dccharacter/RF3Sens/doc/RFSens.sch

## EAGLE design doc/RFSens.sch (2017-03-08)

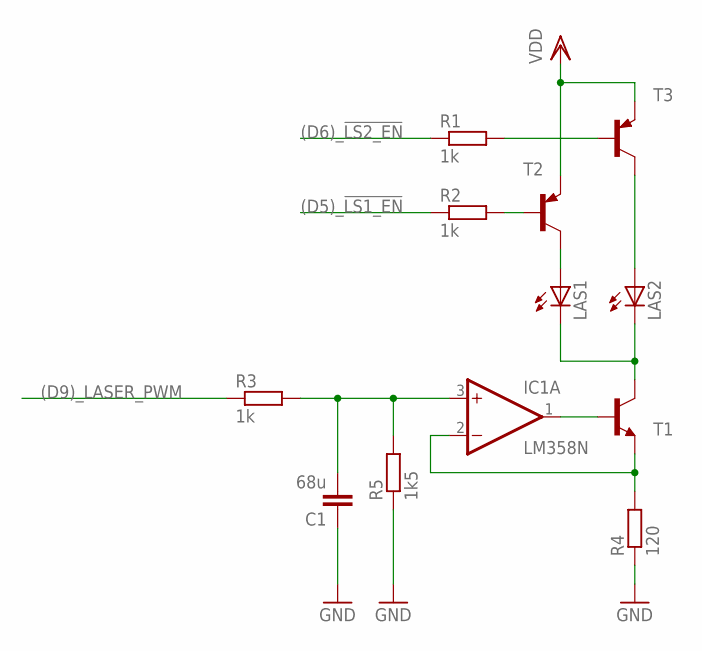
[picture p6: schematic RFSens.sch]

Parts:
C1: 68u; C5B3.5
IC1: LM358N; DIL08
LAS1, LAS2: LED; SMARTLED-TTW
R1, R2, R3: 1k; 0204/5
R4: 120; 0204/5
R5: 1k5; 0204/5
T1: -NPN-SOT89-BCE; SOT89-BCE
T2, T3: -PNP-SOT23-EBC; SOT23-EBC

Connections:
(D5)_!LS1_EN!: R2.1
(D6)_!LS2_EN!: R1.1
(D9)_LASER_PWM: R3.1
GND: C1.1, R4.1, R5.1
unnamed: IC1.2 (-IN), R4.2, T1.E
unnamed: IC1.1 (OUT), T1.B
unnamed: C1.2, IC1.3 (+IN), R3.2, R5.2
unnamed: LAS1.C@1 (C), LAS2.C@1 (C), T1.C
unnamed: R1.2, T3.B
unnamed: LAS2.A@1 (A), T3.C
unnamed: LAS1.A@1 (A), T2.C
unnamed: R2.2, T2.B
VDD: T2.E, T3.E
