dccharacter/RF3Sens/doc/digispark_adns2620.sch

## EAGLE design doc/digispark_adns2620.sch (2016-02-06)

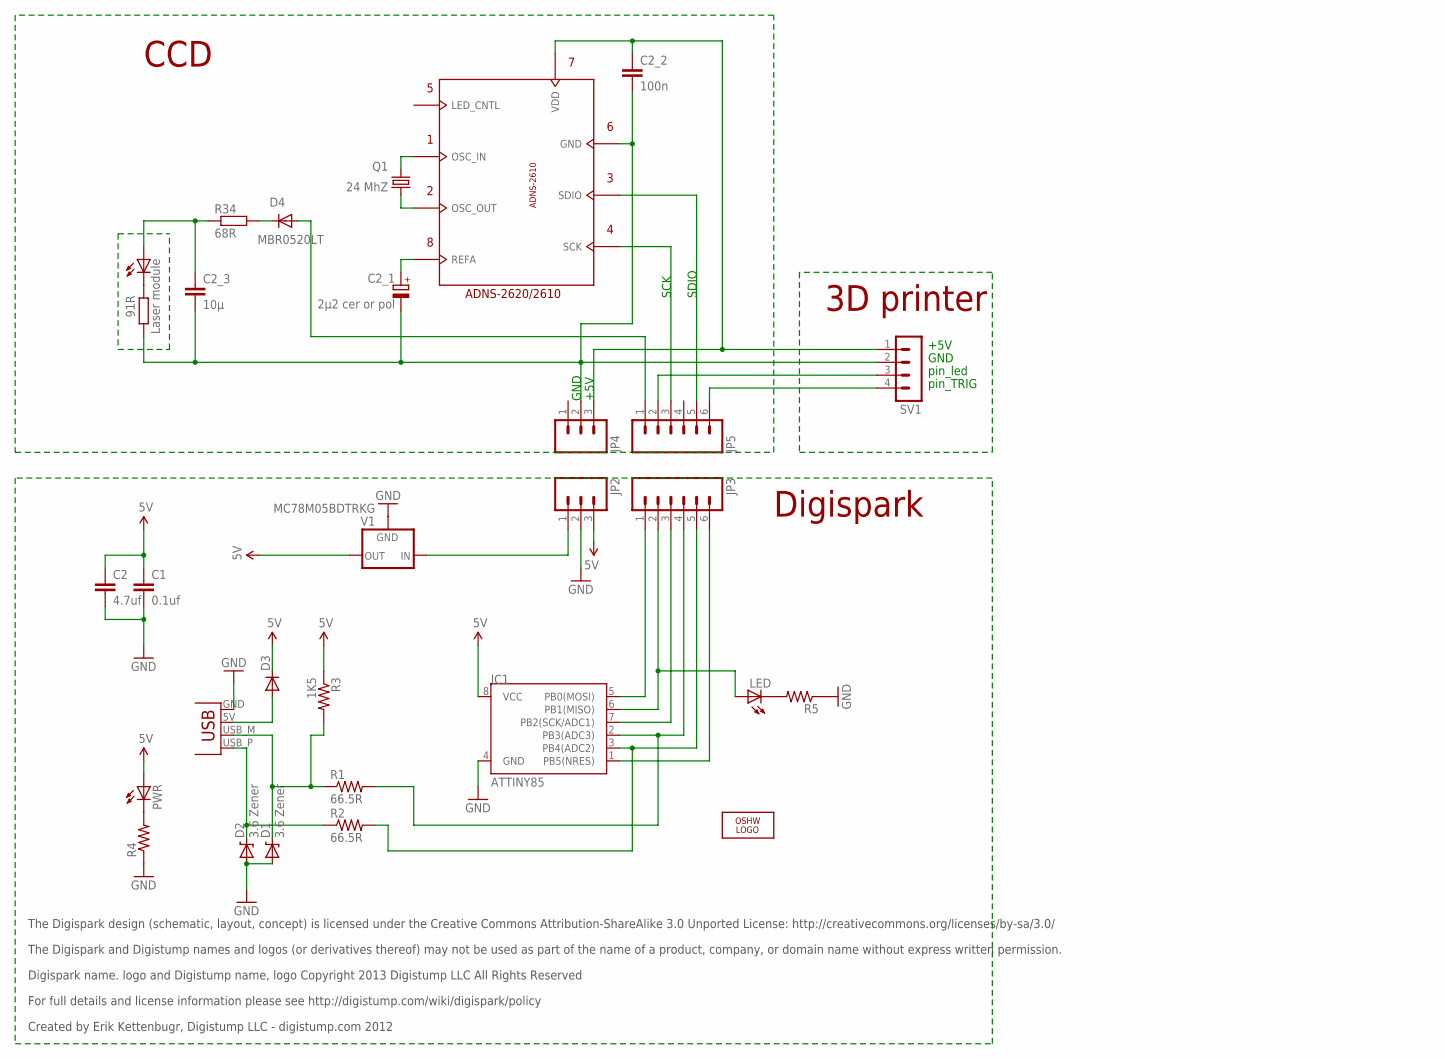
[picture p7: schematic digispark_adns2620.sch]

Parts:
C1: 0.1uf; 0402-CAP
C2: 4.7uf; 0805
C2_1: 2µ2 cer or pol; CT3216
C2_2: 100n; C0805K
C2_3: 10µ; C0805K
D1, D2: 3.6 Zener; SOD-323
D3, D4: MBR0520LT; SOD123
IC1: ATTINY85; SO08-EIAJ
IC2: ADNS-2620/2610; DIP-8_(GORA)
JP2, JP4: M03PTH; 1X03
JP3, JP5: M06SIP; 1X06
LED: LED0603; LED-0603
LED1: Laser module; LED5MM
LOGO2: LOGO-OSHW-10MILX0200-NT; OSHW_10X200_NOTEXT
PWR: LED0603; LED-0603
Q1: 24 MhZ; HC49/S
R1, R2: 66.5R; 0402-RES
R3: 1K5; 0402-RES
R4, R5: RESISTOR0402-RES; 0402-RES
R23: 91R; R1206
R34: 68R; R0805
SV1: MA04-1
V1: MC78M05BDTRKG; DPACK
X1: USBPCB; USB-A-PCB

Connections:
5V: C1.1, C2.1, D3.C, IC1.8 (VCC), JP2.3, PWR.A, R3.1, V1.3 (OUT)
GND: C1.2, C2.2, C2_1.-, C2_2.2, C2_3.2, D1.2 (A), D2.2 (A), IC1.4 (GND), IC2.6 (GND), JP2.2, JP4.2, R4.1, R5.1, R23.1, SV1.2, V1.4 (GND), X1.GND
unnamed: IC1.2 (PB3(ADC3)), JP3.4, R1.2
unnamed: IC1.6 (PB1(MISO)), JP3.2, LED.A
unnamed: IC1.5 (PB0(MOSI)), JP3.1
unnamed: IC1.7 (PB2(SCK/ADC1)), JP3.3
unnamed: IC1.3 (PB4(ADC2)), JP3.5, R2.2
unnamed: JP5.2, SV1.3
unnamed: IC1.1 (PB5(NRES)), JP3.6
unnamed: IC2.4 (SCK), JP5.3
unnamed: D1.1 (C), R1.1, R3.2, X1.USB_M (D-)
unnamed: D2.1 (C), R2.1, X1.USB_P (D+)
unnamed: LED.C, R5.2
unnamed: LED1.K (C), R23.2
unnamed: JP5.6, SV1.4
unnamed: JP2.1, V1.1 (IN)
unnamed: D3.A, X1.5V (VBUS)
unnamed: PWR.C, R4.2
unnamed: IC2.3 (SDIO), JP5.5
unnamed: C2_1.+, IC2.8 (REFA)
unnamed: C2_3.1, LED1.A, R34.1
unnamed: D4.C, R34.2
unnamed: D4.A, JP5.1
unnamed: IC2.1 (OSC_IN), Q1.2
unnamed: IC2.2 (OSC_OUT), Q1.1
VDD: C2_2.1, IC2.7 (VDD), JP4.3, SV1.1

Notes on the sheet:
The Digispark design (schematic, layout, concept) is licensed under the Creative Commons Attribution-ShareAlike 3.0 Unported License: http://creativecommons.org/licenses/by-sa/3.0/
The Digispark and Digistump names and logos (or derivatives thereof) may not be used as part of the name of a product, company, or domain name without express written permission.
Digispark name. logo and Digistump name, logo Copyright 2013 Digistump LLC All Rights Reserved
For full details and license information please see http://digistump.com/wiki/digispark/policy
Created by Erik Kettenbugr, Digistump LLC - digistump.com 2012
SDIO
+5V
GND
SCK
CCD
ADNS-2620/2610
Digispark
pin_led
pin_TRIG
3D printer
