dccharacter/RF3Sens/doc/laser_source_opamp.sch

## EAGLE design doc/laser_source_opamp.sch (2017-09-14)

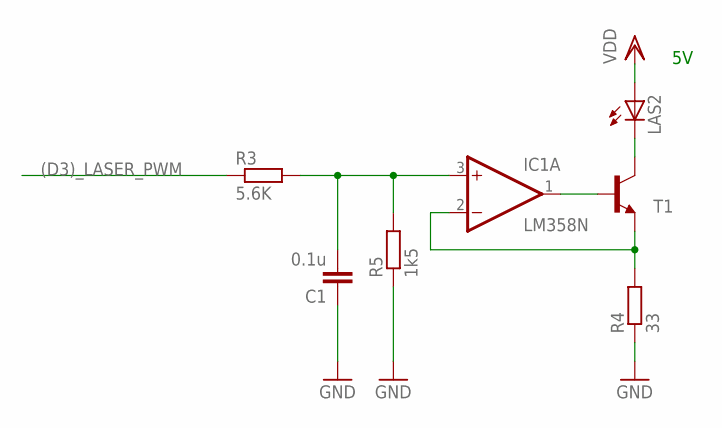
[picture p8: schematic laser_source_opamp.sch]

Parts:
C1: 0.1u; C5B3.5
IC1: LM358N; DIL08
LAS2: LED; SMARTLED-TTW
R3: 5.6K; 0204/5
R4: 33; 0204/5
R5: 1k5; 0204/5
T1: -NPN-SOT89-BCE; SOT89-BCE

Connections:
(D3)_LASER_PWM: R3.1
GND: C1.1, R4.1, R5.1
unnamed: IC1.2 (-IN), R4.2, T1.E
unnamed: IC1.1 (OUT), T1.B
unnamed: C1.2, IC1.3 (+IN), R3.2, R5.2
unnamed: LAS2.C@1 (C), T1.C
VDD: LAS2.A@1 (A)
